dumcatt/SDVX-ProModel/DXFs/BottomCover.dxf

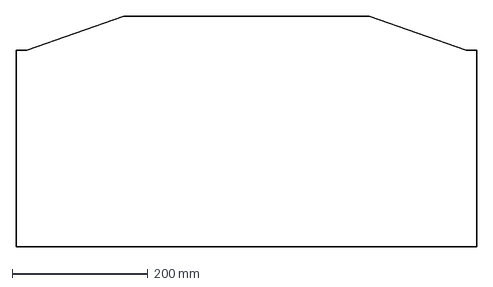
[picture p15: CAD file, 2026-09-29]
DXFs/BottomCover.dxf
680.0 x 340.0 mm
