dumcatt/SDVX-ProModel/DXFs/Back.dxf

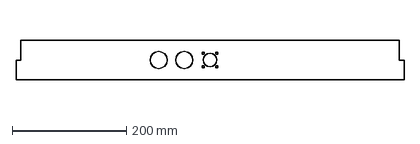
[picture p16: CAD file, 2026-09-29]
DXFs/Back.dxf
680.0 x 70.0 mm
